lmurach/AU_Capstone_Trideum/allFrameParts/RFID Door/RFID Door Frame (x1).stl

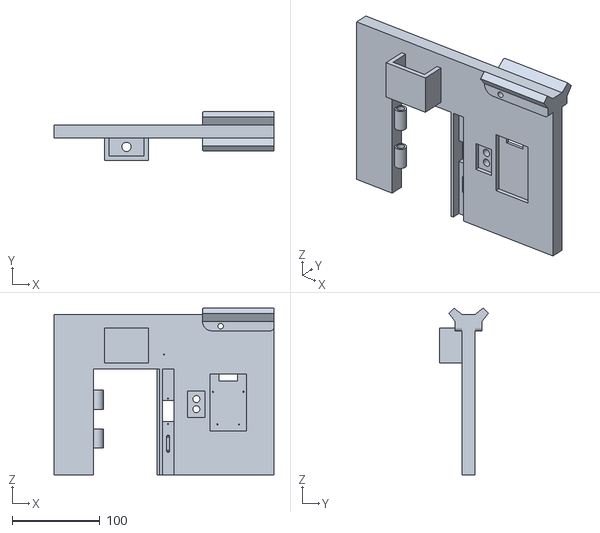
[picture p17: CAD file, 2024-05-01]
allFrameParts/RFID Door/RFID Door Frame (x1).stl
250.1 x 55.5 x 189.8
