lmurach/AU_Capstone_Trideum/allFrameParts/Wire Concealment/NeoPixel Cover (x3).stl

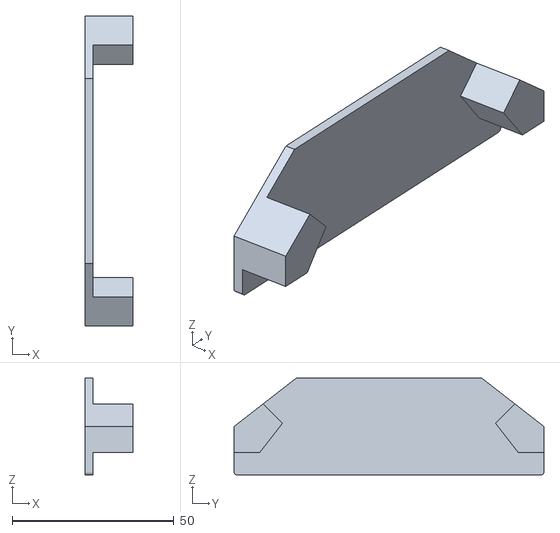
[picture p18: CAD file, 2024-05-01]
allFrameParts/Wire Concealment/NeoPixel Cover (x3).stl
15.0 x 95.9 x 30.0
