lmurach/AU_Capstone_Trideum/allFrameParts/Wire Floor/Wire Cover Panel Short (x1).stl

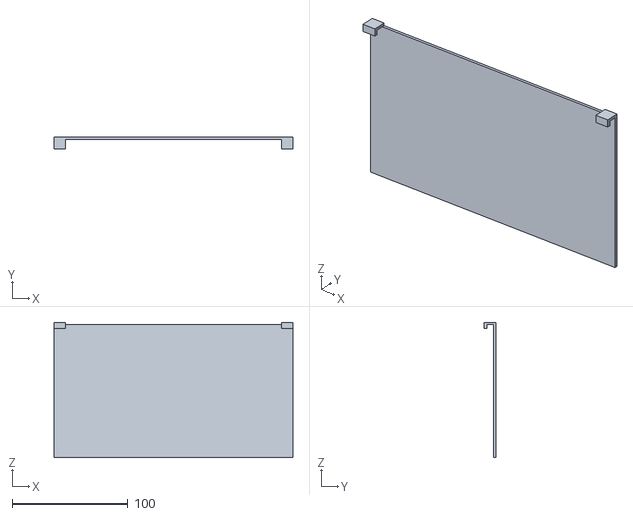
[picture p19: CAD file, 2024-05-01]
allFrameParts/Wire Floor/Wire Cover Panel Short (x1).stl
206.4 x 10.0 x 117.0
