lmurach/AU_Capstone_Trideum/allFrameParts/Base Frame/Support Beam 4mm, 100mm (x4).stl

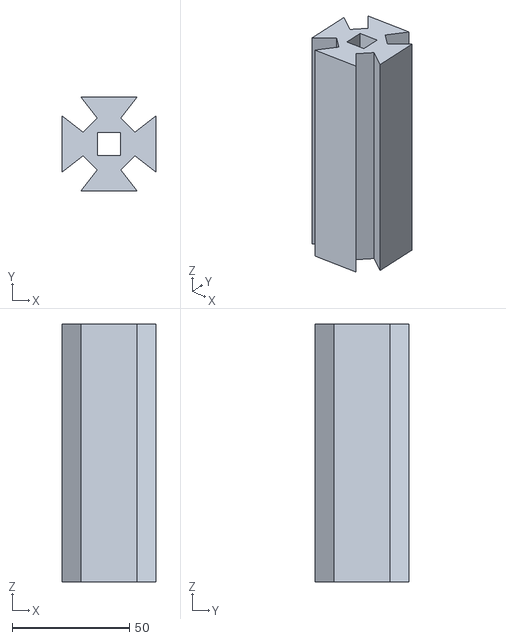
[picture p20: CAD file, 2024-05-01]
allFrameParts/Base Frame/Support Beam 4mm, 100mm (x4).stl
40.0 x 40.0 x 110.0
