lmurach/AU_Capstone_Trideum/allFrameParts/Elevator/Push Button Mount (x3).stl

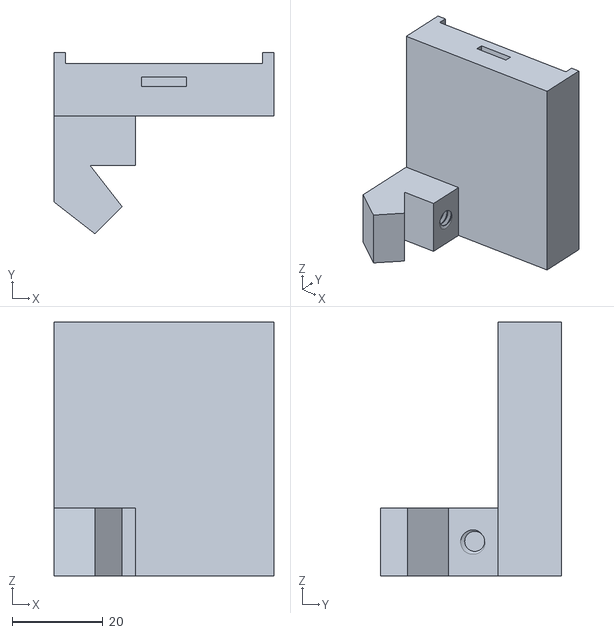
[picture p21: CAD file, 2024-05-01]
allFrameParts/Elevator/Push Button Mount (x3).stl
48.5 x 40.0 x 56.0
