lmurach/AU_Capstone_Trideum/allFrameParts/HVAC Duct System/HVAC Duct 6 (x1).stl

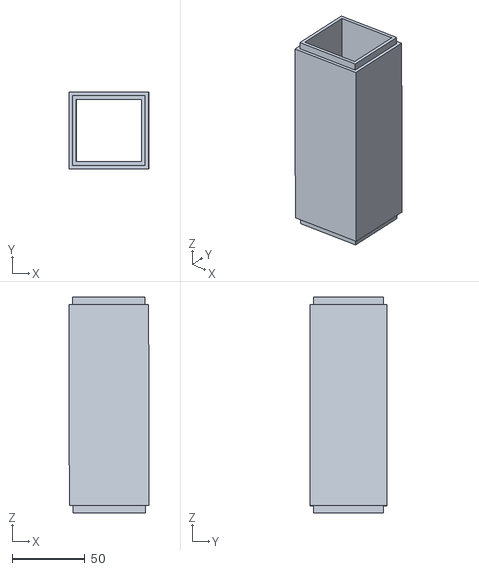
[picture p22: CAD file, 2024-05-01]
allFrameParts/HVAC Duct System/HVAC Duct 6 (x1).stl
55.4 x 53.0 x 148.7
