lmurach/AU_Capstone_Trideum/allFrameParts/Wire Concealment/Wire Channel F1 R (x1).stl

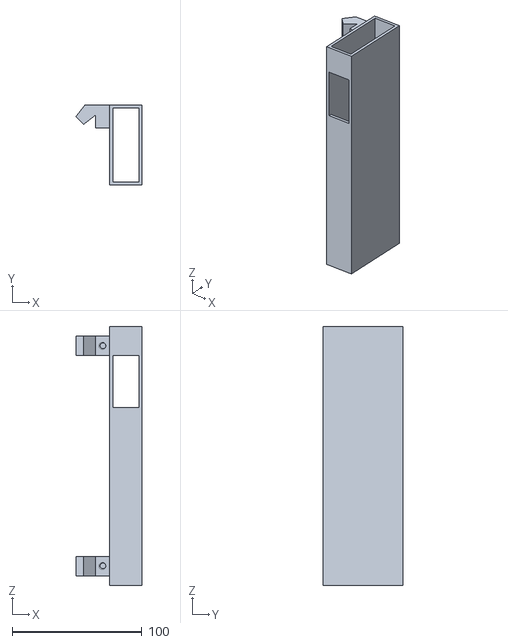
[picture p23: CAD file, 2024-05-01]
allFrameParts/Wire Concealment/Wire Channel F1 R (x1).stl
51.0 x 62.0 x 200.0
