lmurach/AU_Capstone_Trideum/allFrameParts/Wire Floor/Wire Cover Panel Long (x2).stl

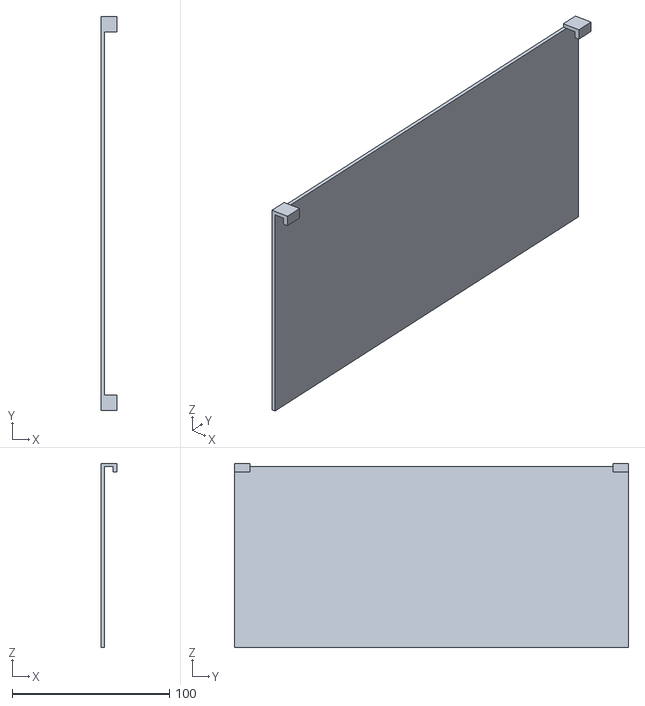
[picture p24: CAD file, 2024-05-01]
allFrameParts/Wire Floor/Wire Cover Panel Long (x2).stl
10.0 x 250.3 x 117.0
