lmurach/AU_Capstone_Trideum/allFrameParts/Base Frame/Support Beam 4mm, 200mm (x12).stl

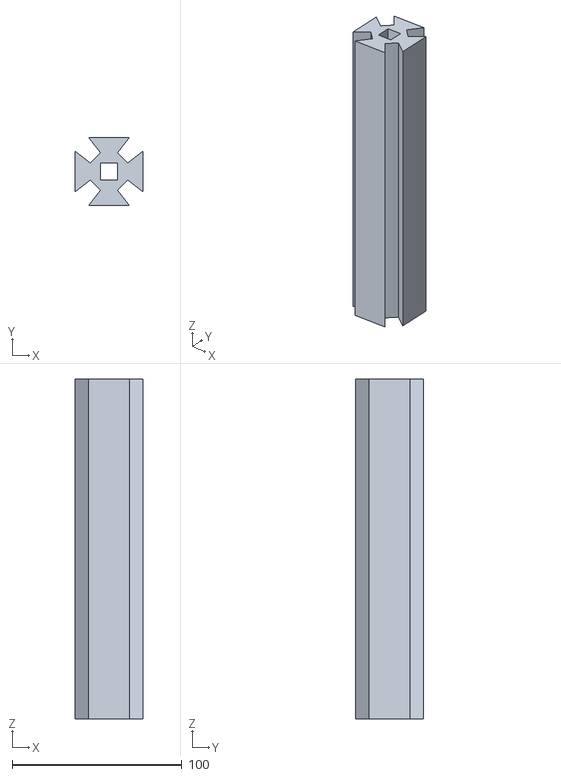
[picture p25: CAD file, 2024-05-01]
allFrameParts/Base Frame/Support Beam 4mm, 200mm (x12).stl
40.0 x 40.0 x 200.0
