lmurach/AU_Capstone_Trideum/allFrameParts/HVAC Duct System/HVAC Duct 1 (x1).stl

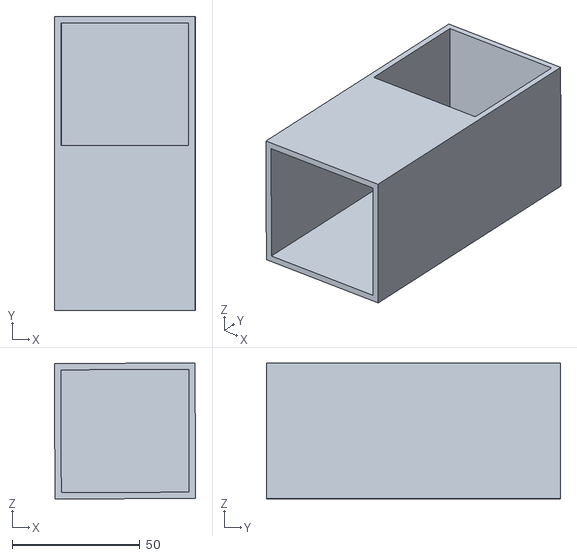
[picture p26: CAD file, 2024-05-01]
allFrameParts/HVAC Duct System/HVAC Duct 1 (x1).stl
55.2 x 115.0 x 53.2
