lmurach/AU_Capstone_Trideum/allFrameParts/Base Frame/Base Frame Clamp L (x2).stl

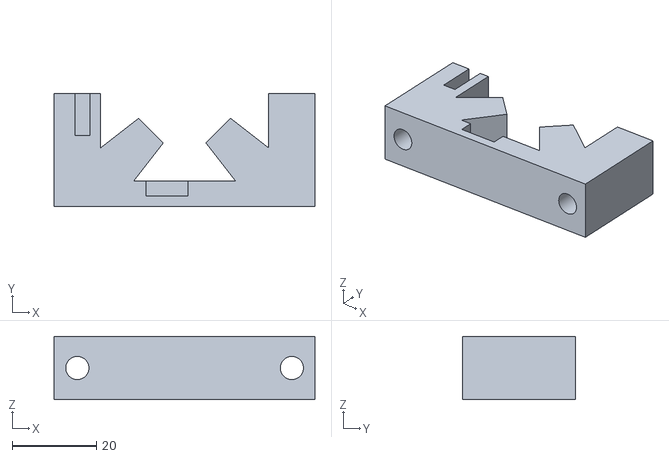
[picture p28: CAD file, 2024-05-01]
allFrameParts/Base Frame/Base Frame Clamp L (x2).stl
62.0 x 26.8 x 15.0
