lmurach/AU_Capstone_Trideum/allFrameParts/HVAC Duct System/HVAC Duct 7 (x1).stl

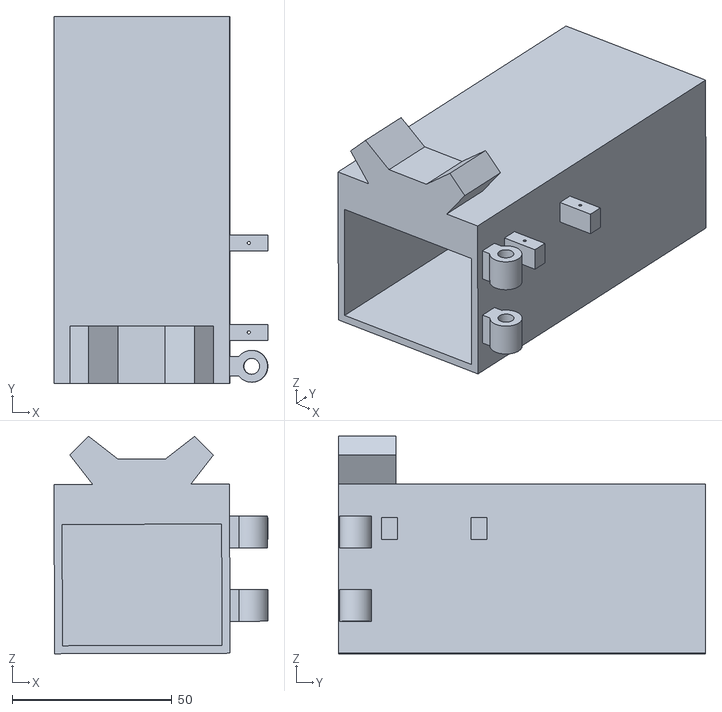
[picture p29: CAD file, 2024-05-01]
allFrameParts/HVAC Duct System/HVAC Duct 7 (x1).stl
67.1 x 115.0 x 68.2
