lmurach/AU_Capstone_Trideum/allFrameParts/Wire Concealment/Wire Channel F2 R (x1).stl

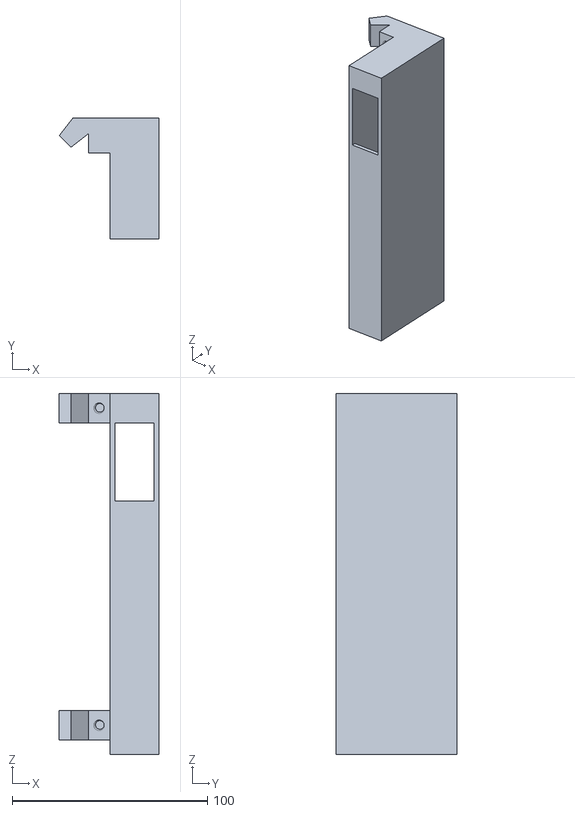
[picture p30: CAD file, 2024-05-01]
allFrameParts/Wire Concealment/Wire Channel F2 R (x1).stl
51.0 x 62.0 x 185.0
