lmurach/AU_Capstone_Trideum/allFrameParts/Wire Floor/Arduino Peg Mount (x1).stl

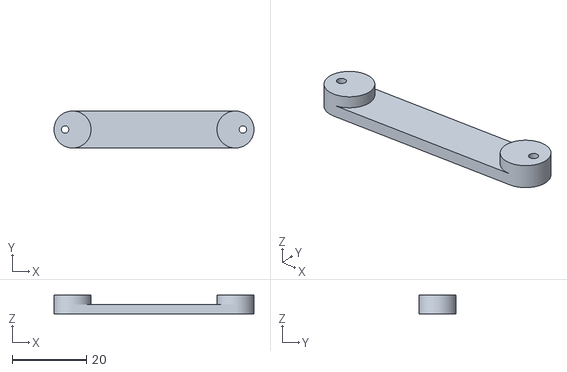
[picture p31: CAD file, 2024-05-01]
allFrameParts/Wire Floor/Arduino Peg Mount (x1).stl
54.0 x 10.0 x 5.00
