lmurach/AU_Capstone_Trideum/allFrameParts/Base Frame/Basement Floor (x1).stl

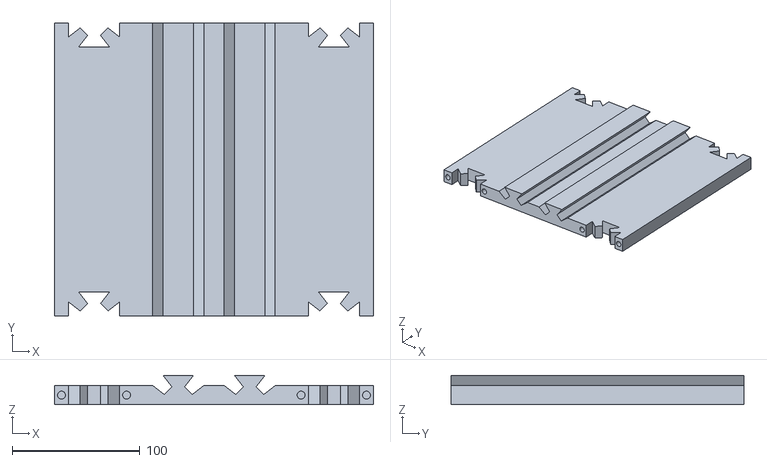
[picture p32: CAD file, 2024-05-01]
allFrameParts/Base Frame/Basement Floor (x1).stl
250.0 x 229.9 x 23.0
