lmurach/AU_Capstone_Trideum/allFrameParts/Wire Concealment/Push Button Cover 3 (x1).stl

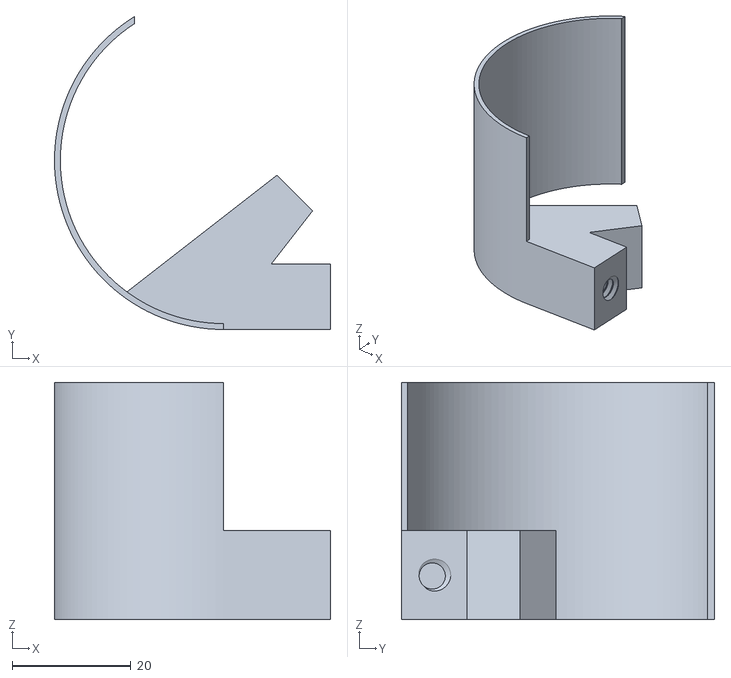
[picture p34: CAD file, 2024-05-01]
allFrameParts/Wire Concealment/Push Button Cover 3 (x1).stl
46.5 x 52.7 x 40.0
