lmurach/AU_Capstone_Trideum/allFrameParts/Base Frame/Base Frame Clamp (x16).stl

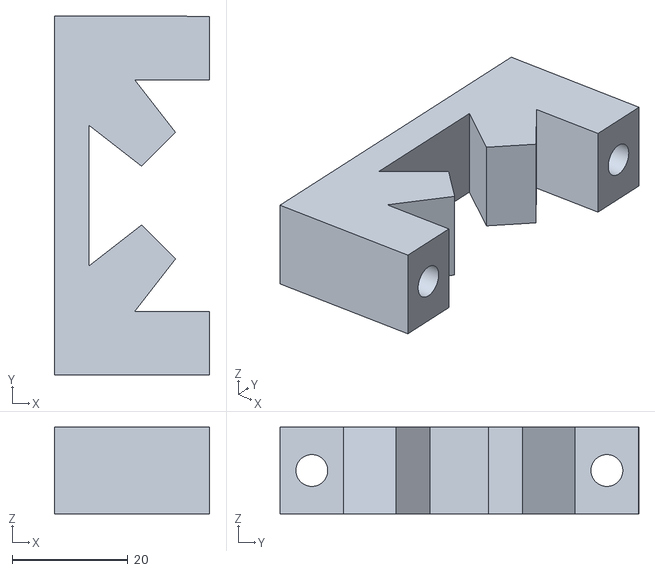
[picture p35: CAD file, 2024-05-01]
allFrameParts/Base Frame/Base Frame Clamp (x16).stl
26.8 x 62.0 x 15.0
