lmurach/AU_Capstone_Trideum/allFrameParts/Wire Concealment/Push Button Cover 2 (x1).stl

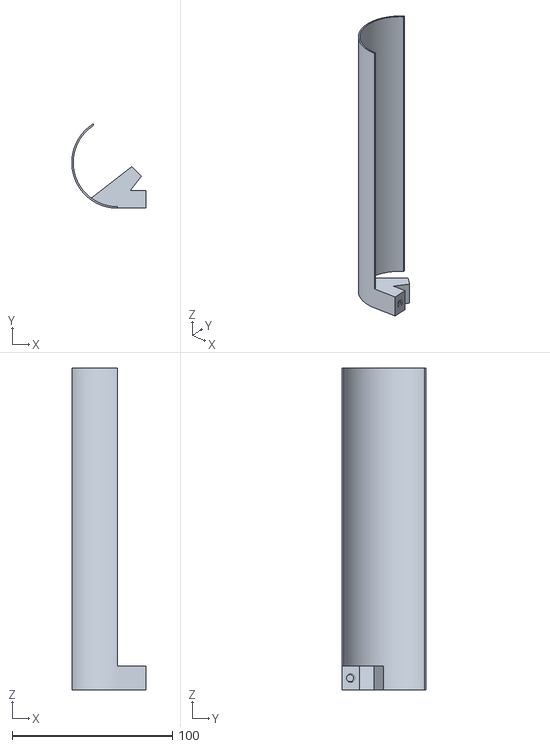
[picture p36: CAD file, 2024-05-01]
allFrameParts/Wire Concealment/Push Button Cover 2 (x1).stl
46.5 x 52.7 x 201.0
