lmurach/AU_Capstone_Trideum/allFrameParts/HVAC Duct System/HVAC Duct 2 (x1).stl

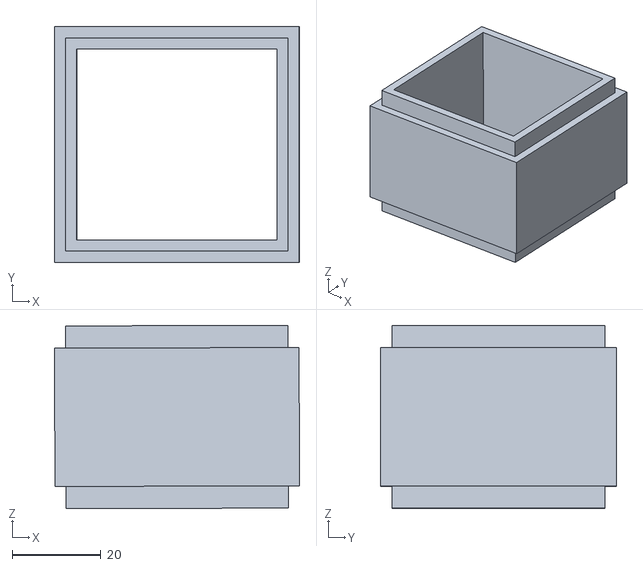
[picture p37: CAD file, 2024-05-01]
allFrameParts/HVAC Duct System/HVAC Duct 2 (x1).stl
55.1 x 53.0 x 41.3
