lmurach/AU_Capstone_Trideum/allFrameParts/Base Frame/Wire Floor Base (x1).stl

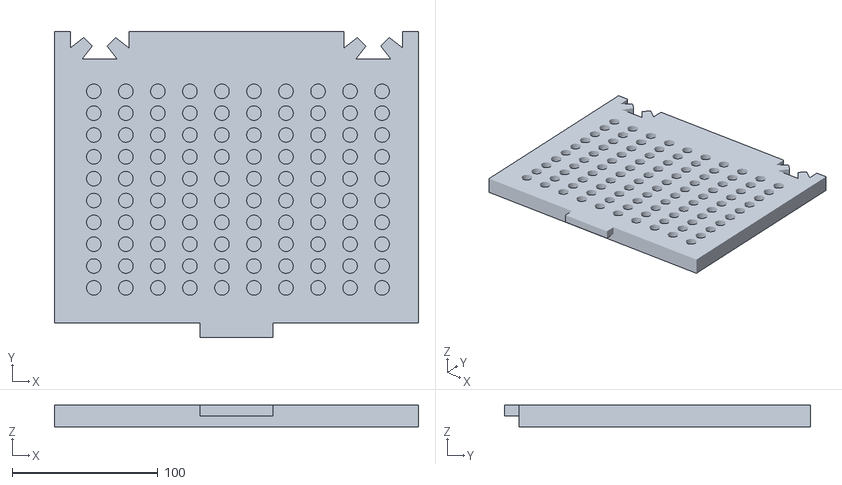
[picture p38: CAD file, 2024-05-01]
allFrameParts/Base Frame/Wire Floor Base (x1).stl
250.0 x 210.0 x 15.0
