lmurach/AU_Capstone_Trideum/allFrameParts/HVAC Duct System/HVAC Duct 4 (x1).stl

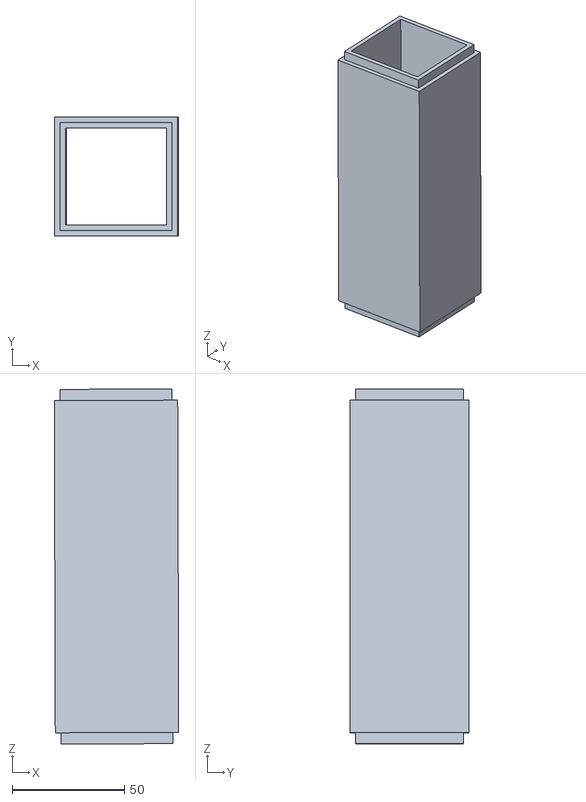
[picture p39: CAD file, 2024-05-01]
allFrameParts/HVAC Duct System/HVAC Duct 4 (x1).stl
55.4 x 53.0 x 158.1
