lmurach/AU_Capstone_Trideum/background_main.py

""" 
Author  : Lauren Murach
Date    : 02/27/2024
Purpose : This is the main class to operate as a scheduler. Later in time 
          concurrency will be added.
"""
import time
import serial
from PyQt5.QtCore import QRunnable, pyqtSlot, pyqtSignal, QObject, QThread
import RPi.GPIO as GPIO
from RFID import RFIDSecurity
from neo_pixel_motion import NeoPixelMotion
from door import Door
from database import Database
from tempSensor import TempControl
from door_lights import DoorLights

class BackgroundMain(QObject):
    '''This serves as the "main" function for everything that is not the GUI.
    Another file keeps all the threading functions related to the background 
    processes for seperation of concerns.
    
    Concurrency model: 2 threads, GUI and background. *Maybe* 3 with the arduino
    elevator. There is a maximum of 4 threads so keeping everything on different
    threads could lead to long delays and a high possibility of a non-responsive
    GUI (if 4 threads activate so the GUI is put on the queue)'''

    logs_changed = pyqtSignal()
    temp_signal = pyqtSignal(int, int, bool)
    motion_signal = pyqtSignal(int, str)
    button_signal = pyqtSignal(list)

    rfid = RFIDSecurity()
    door = Door()
    door.GPIO_init()

    def __init__(self):
        super().__init__()
        GPIO.setmode(GPIO.BCM)
        self.motion_sensor_0 = NeoPixelMotion(0, 12)
        self.motion_sensor_1 = NeoPixelMotion(1, 16)
        self.motion_sensor_2 = NeoPixelMotion(2, 20)
        self.motionsensors = [
            self.motion_sensor_0,
            self.motion_sensor_1,
            self.motion_sensor_2
        ]
        self.temp_sensor_0 = TempControl(0, 0x48)
        self.temp_sensor_1 = TempControl(1, 0x49)
        self.temp_sensor_2 = TempControl(2, 0x4D)
        self.temp_sensors = [
            self.temp_sensor_0,
            self.temp_sensor_1,
            self.temp_sensor_2
        ]
        self.temp_sensor_turn = 1

        self.ser = serial.Serial('/dev/ttyACM0', 115200, timeout=1)
        self.ser.reset_input_buffer()

        self.running = True

    def run(self):
        '''Main thread'''

        while self.running:
            self._RFID_handler()
            self._door_handler()
            #print(self.door._is_door_closed())
            self._light_handler()
            self._temp_handler()
            DoorLights.handle_turning_off_lights()
            self._update_elevator()
            time.sleep(0.2)

    # @pyqtSlot()
    # def run(self):
    #     '''Main thread'''
    #     while True:
    #         # All door and RFID code is here
    #         self._RFID_handler()
    #         self._door_handler()
    #         self._light_handler()
    #         time.sleep(0.1)

    #     # while True:
    #     #     Database.set_temperature(0, 72)
    #     #     time.sleep(0.1)

    def _RFID_handler(self):
        if self.rfid.is_card_there():
            (validity, e_id) = self.rfid.handle_read_card()
            # for _ in range (0, 20):
            #     self.rfid.is_card_there()
            if validity:
                self.door.card_owner_id = e_id

    def _door_handler(self):
        if self.door.card_owner_id is not None:
            if self.door.handle_lock():
                self.logs_changed.emit()

    def _light_handler(self):
        for num, sensor in enumerate(self.motionsensors):
            if sensor.motion_is_detected():
                if sensor.is_time():
                    sensor.turn_on_lights()
                    self.motion_signal.emit(num, "on")
                    self.logs_changed.emit()
            else:
                sensor.turn_off_lights()
                self.motion_signal.emit(num, "off")

    def _temp_handler(self):
        hvac_on = False
        for sensor in self.temp_sensors:
            is_changed, temp = sensor.get_temp_if_changed()
            if is_changed:
                self.logs_changed.emit()
            if temp == sensor.TEMP_ERROR_VAL:
                self.temp_signal.emit(sensor.floor, 0, False)
            else:
                self.temp_signal.emit(sensor.floor, temp, True)
            if sensor.prev_HVAC_is_on:
                hvac_on = True
            # print(f"f:{sensor.floor} hvac status: {sensor.prev_HVAC_is_on}")
        TempControl.change_HVAC_cooler_state(hvac_on)
        if TempControl.servo_busy_counter == 0:
            TempControl.servo_turn = (TempControl.servo_turn + 1 ) % len(self.temp_sensors)
        else:
            TempControl.servo_busy_counter -= 1
            # Fake Data:
            # temp = self.temp_sensor.read_fake_temp(self.temp_sensor.floor1_address)
            # self.temp_signal.emit(1, temp)
            # temp = self.temp_sensor.read_fake_temp(self.temp_sensor.floor2_address)
            # self.temp_signal.emit(2, temp)

    def _update_elevator(self):
        """ This method will read the state of the elevator from the serial port"""
                # If there are messages to read.
        if (self.ser.in_waiting>0):

            # Read the starting bit.
            start = self.ser.readline().decode('utf-8').rstrip()

            # check to ensure the start is the start.
            if (start == "S"):

                # Read the next three lines that represent the state of our requested queue.
                bs1 = self.ser.readline().decode('utf-8').rstrip()
                bs2 = self.ser.readline().decode('utf-8').rstrip()
                bs3 = self.ser.readline().decode('utf-8').rstrip()
                current_floor = self.ser.readline().decode('utf-8').rstrip()

                # read the last byte and make sure it is the ending byte. 
                end = self.ser.readline().decode('utf-8').rstrip()

                if (end == "E"):
                    # Emit the queue to the GUI
                    self.button_signal.emit([int(bs1), int(bs2), int(bs3), int(current_floor)])
